flupes/catdoor/data/PWM_93KHz_25pc_M0out.png

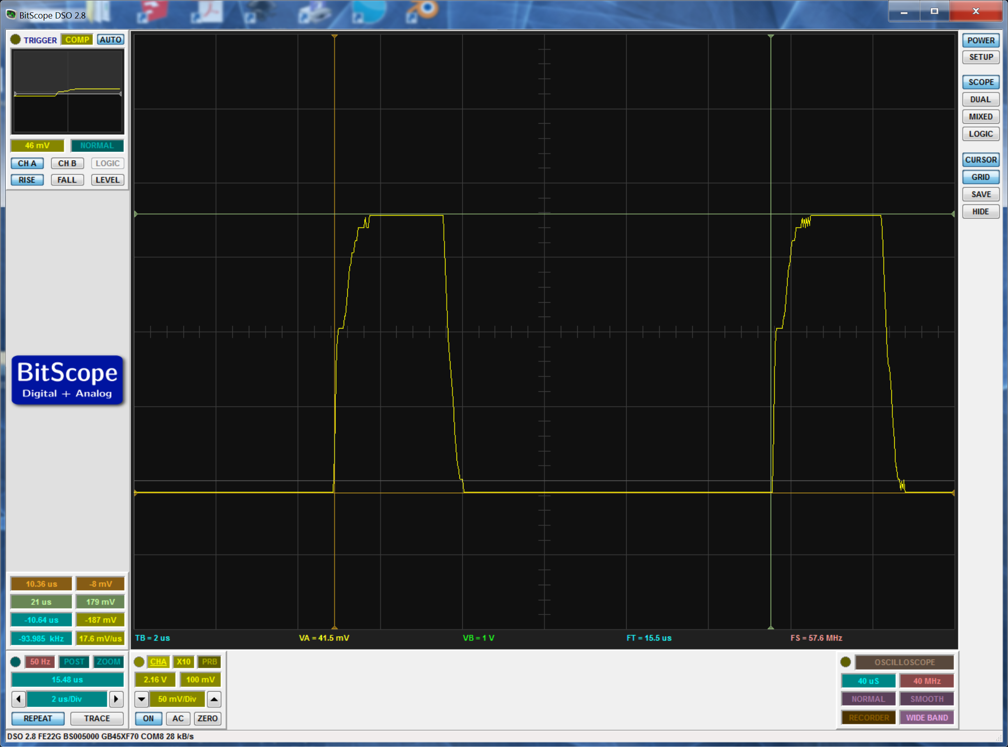
data/PWM_93KHz_25pc_M0out.png
