flupes/catdoor/data/PWM_93KHz_25pc_MOSFETout.png

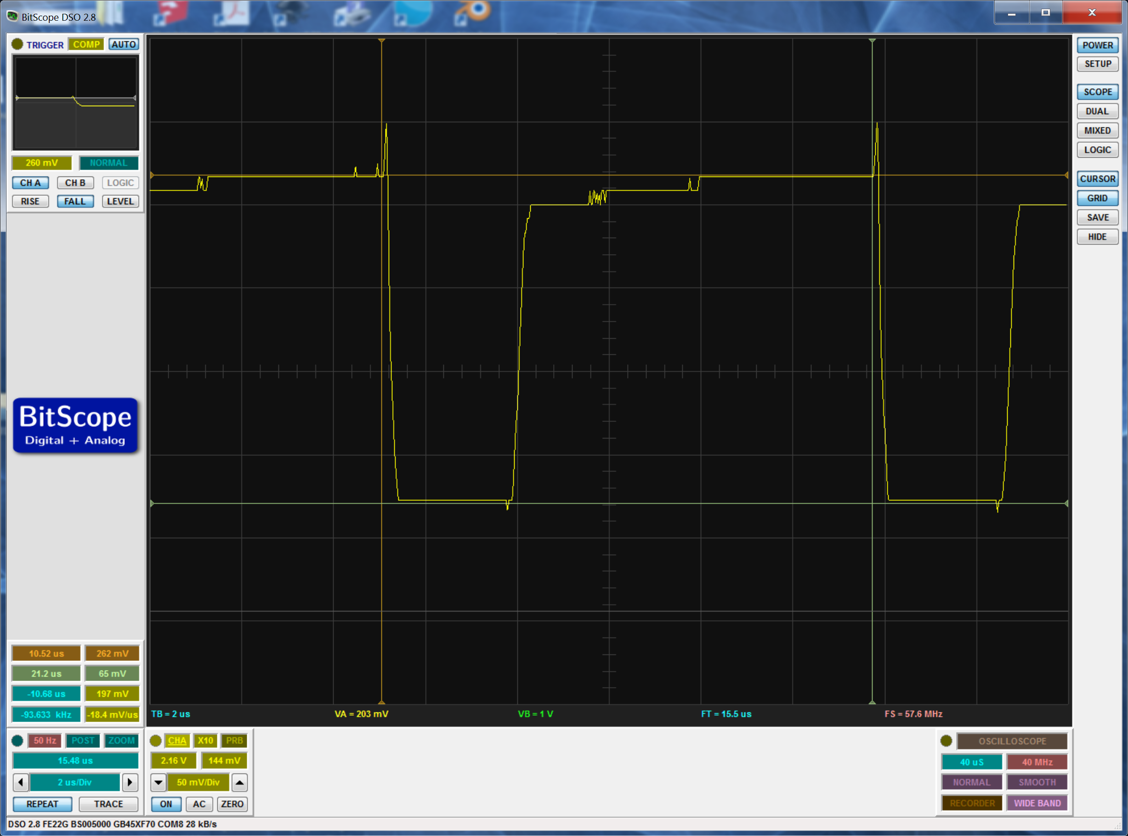
data/PWM_93KHz_25pc_MOSFETout.png
