flupes/catdoor/catdoor_v2/tests/accel/data/in_limits.csv

Testing Accelerometer - Take 4
LIS3DH found!
-15968 | 1632
-16016 | 1680
-16032 | 1648
-16016 | 1680
-16016 | 1664
-16016 | 1616
-16064 | 1632
-16080 | 1664
-16064 | 1664
-16000 | 1632
-16048 | 1520
-16096 | 1632
-16096 | 1696
-16096 | 1632
-16064 | 1616
-16048 | 1664
-16016 | 1536
-16032 | 1520
-15968 | 1568
-15968 | 1616
-16032 | 1520
-16064 | 1632
-16048 | 1568
-16016 | 1568
-16048 | 1568
-16080 | 1664
-16016 | 1648
-16032 | 1600
-16096 | 1584
-16080 | 1600
-16080 | 1584
-16096 | 1632
-16048 | 1600
-16096 | 1632
-16048 | 1632
-16080 | 1600
-16064 | 1632
-16080 | 1632
-16080 | 1648
-16080 | 1616
-16080 | 1680
-16064 | 1632
-16048 | 1648
-16016 | 1664
-16048 | 1632
-16048 | 1680
-16016 | 1632
-16032 | 1632
-16016 | 1648
-16080 | 1584
-16032 | 1584
-16080 | 1616
-16048 | 1616
-16000 | 1584
-16016 | 1616
-16096 | 1584
-16048 | 1648
-16032 | 1648
-16064 | 1616
-16080 | 1664
-16096 | 1600
-16096 | 1600
-16112 | 1600
-16112 | 1632
-16112 | 1664
-16064 | 1632
-16096 | 1696
-16112 | 1664
-16096 | 1680
-16112 | 1680
-16080 | 1664
-16016 | 1680
-16048 | 1616
-16096 | 1568
-16080 | 1568
-16048 | 1600
-16032 | 1584
-16032 | 1616
-16064 | 1616
-16128 | 1632
-16144 | 1616
-16080 | 1664
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
