flupes/catdoor/catdoor_v2/tests/publisher/src/main.cpp

#include "RTClib.h"
#include "daytimes.h"
#include "ledctrl.h"
#include "m0_hf_pwm.h"
#include "mqtt_client.h"
#include "netcfg.h"
#include "utils.h"
#include "watchdog_timer.h"

RTC_DS3231 rtc;
char buffer[64];

LedCtrl& status_led = LedCtrl::Instance();
WiFiClient wifi_client;
MQTT_Client mqtt_client(wifi_client, status_led);

void setup() {
  Serial.begin(115200);
  while (!Serial) {
    ;  // wait for serial port to connect. Needed for native USB port only
  }
  Serial.println("Start MQTT Publisher...");
  if (!rtc.begin()) {
    Serial.println("Couldn't find RTC!");
    while (1)
      ;
  }
  // HF PWM
  pwm_configure();

  wdt_configure(11);

  // start in unkown state
  status_led.warning();

  // Configure pins for Adafruit ATWINC1500 Feather
  WiFi.setPins(8, 7, 4, 2);
  // Check for the presence of the shield
  PRINTLN("Connecting to the Wifi Module");
  if (WiFi.status() == WL_NO_SHIELD) {
    PRINTLN("WiFi shield not present");
    return;  // don't continue
  }
  mqtt_client.connect_wifi(MY_WIFI_SSID, MY_WIFI_PASS);
  mqtt_client.setServer(MQTT_SERVER, MQTT_PORT);
  mqtt_client.connect_client();

  wdt_configure(5);

  DateTime utc_time = rtc.now();
  unsigned int now = millis();
  DateTime local_time = utc_time.getLocalTime(TIME_ZONE_OFFSET);
  mqtt_client.sync_time(local_time, now);
}

static const unsigned long PERIOD = 20;

Timing perf("TIMER", 1);

void loop() {
  static int counter = 0;
  static bool daylight = false;
  static unsigned long last_time = millis();

  unsigned long now = millis();
  if ((now - last_time) > 10 * 1000) {
    DateTime utc = rtc.now();
    DateTime local = utc.getLocalTime(TIME_ZONE_OFFSET);
    uint16_t day = local.yDay();
    if (day == 366) day = 1;  // We will be one day offset for all leap years...
    DateTime sunrise(local.year(), local.month(), local.day(),
                     sunset_sunrise_times[day - 1][0],
                     sunset_sunrise_times[day - 1][1], 0, TIME_ZONE_OFFSET);
    DateTime sunset(local.year(), local.month(), local.day(),
                    sunset_sunrise_times[day - 1][2],
                    sunset_sunrise_times[day - 1][3], 0, TIME_ZONE_OFFSET);

    if (true || (sunrise < local && local < sunset)) {
      if (!daylight) {
        daylight = true;
        status_led.ok();
      }
    } else {
      daylight = false;
      status_led.alive();
    }
    perf.start();
    char msg[8];
    if (daylight) {
      strcpy(msg, "OPEN");
    } else {
      strcpy(msg, "CLOSED");
    }
    unsigned int now = millis();
    mqtt_client.publish_timed_msg(now, TOPIC_HEARTBEAT, msg);
    perf.stop();
    last_time = now;
  }

  // Let the MQTT client do some work
  mqtt_client.loop();

  wdt_reset();

  delay(PERIOD);

  counter++;
}
