flupes/catdoor/catdoor_lt/test/bbb_mqtt/src/netcfg.h

#ifndef _NET_CFG_H_
#define _NET_CFG_H_

// The ESP was nice since we could store the configuration in EEPROM...
// Alas, just put our secrets here!
#define MY_WIFI_SSID "********"
#define MY_WIFI_PASS "********"
#define MQTT_SERVER "xxx.xx.0.xx"
#define MQTT_PORT 1883

#endif
